larkvi/SimpleRTIDome/examples/v2/batch_010_onebirrcoin/010_09_rti.jpg

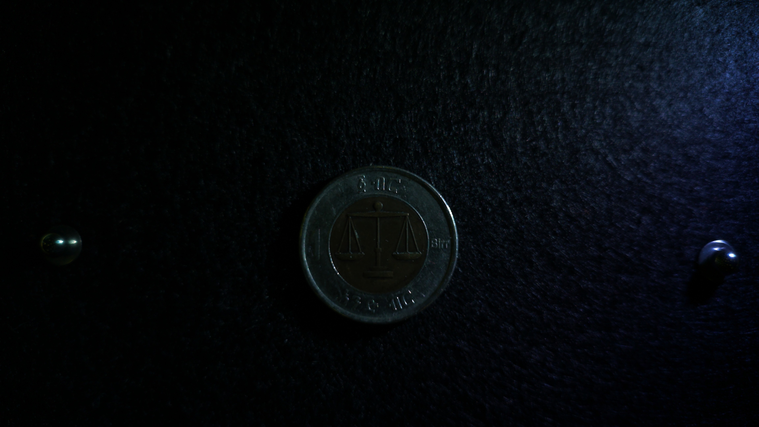
examples/v2/batch_010_onebirrcoin/010_09_rti.jpg
