larkvi/SimpleRTIDome/examples/v2/batch_010_onebirrcoin/010_17_rti.jpg

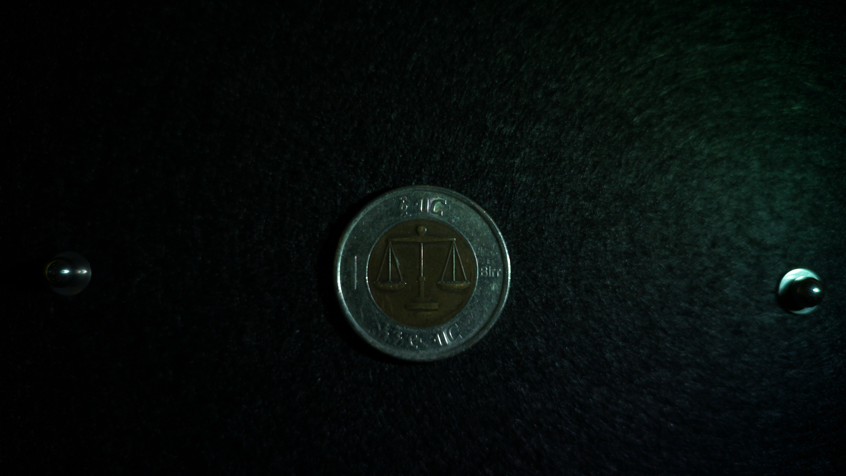
examples/v2/batch_010_onebirrcoin/010_17_rti.jpg
