larkvi/SimpleRTIDome/examples/v2/batch_010_onebirrcoin/010_19_rti.jpg

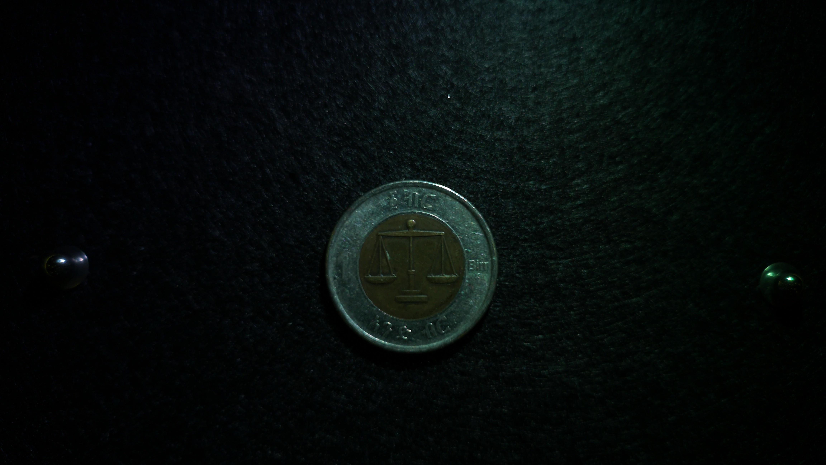
examples/v2/batch_010_onebirrcoin/010_19_rti.jpg
