larkvi/SimpleRTIDome/examples/v2/batch_010_onebirrcoin/010_22_rti.jpg

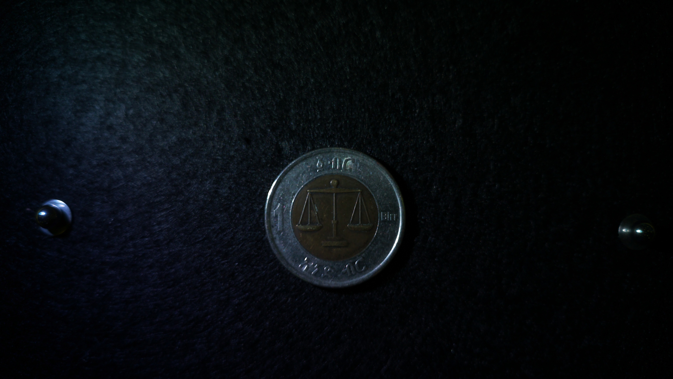
examples/v2/batch_010_onebirrcoin/010_22_rti.jpg
