larkvi/SimpleRTIDome/examples/v2/batch_010_onebirrcoin/010_40_rti.jpg

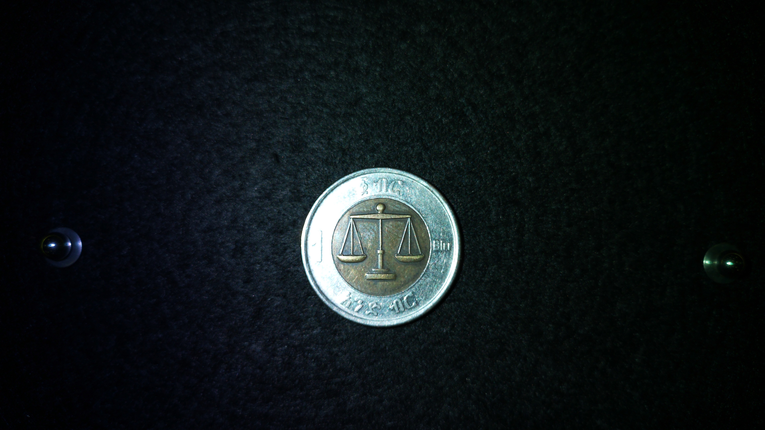
examples/v2/batch_010_onebirrcoin/010_40_rti.jpg
