larkvi/SimpleRTIDome/examples/v2/batch_010_onebirrcoin/output/plane_0_files/3/1_0.jpg

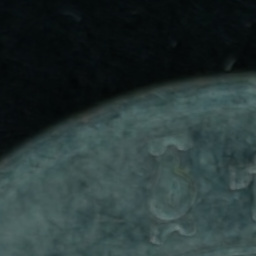
examples/v2/batch_010_onebirrcoin/output/plane_0_files/3/1_0.jpg
