larkvi/SimpleRTIDome/examples/v2/batch_010_onebirrcoin/output/plane_0_files/3/1_3.jpg

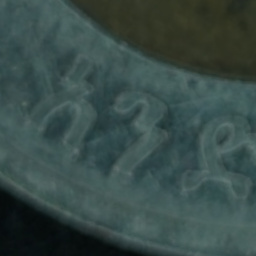
examples/v2/batch_010_onebirrcoin/output/plane_0_files/3/1_3.jpg
