larkvi/SimpleRTIDome/examples/v2/batch_010_onebirrcoin/output/plane_0_files/3/2_2.jpg

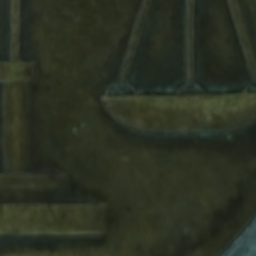
examples/v2/batch_010_onebirrcoin/output/plane_0_files/3/2_2.jpg
