larkvi/SimpleRTIDome/examples/v2/batch_010_onebirrcoin/output/plane_1_files/2/0_1.jpg

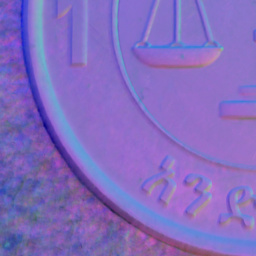
examples/v2/batch_010_onebirrcoin/output/plane_1_files/2/0_1.jpg
