larkvi/SimpleRTIDome/examples/v2/batch_010_onebirrcoin/output/plane_1_files/2/1_0.jpg

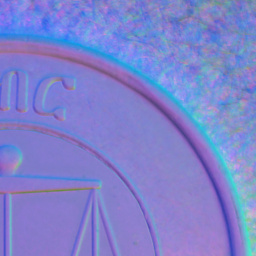
examples/v2/batch_010_onebirrcoin/output/plane_1_files/2/1_0.jpg
