larkvi/SimpleRTIDome/examples/v2/batch_010_onebirrcoin/output/plane_1_files/3/0_0.jpg

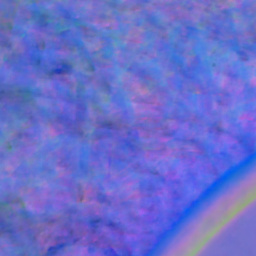
examples/v2/batch_010_onebirrcoin/output/plane_1_files/3/0_0.jpg
