larkvi/SimpleRTIDome/examples/v2/batch_010_onebirrcoin/output/plane_1_files/3/1_1.jpg

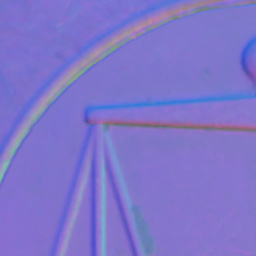
examples/v2/batch_010_onebirrcoin/output/plane_1_files/3/1_1.jpg
