larkvi/SimpleRTIDome/examples/v2/batch_010_onebirrcoin/output/plane_2.jpg

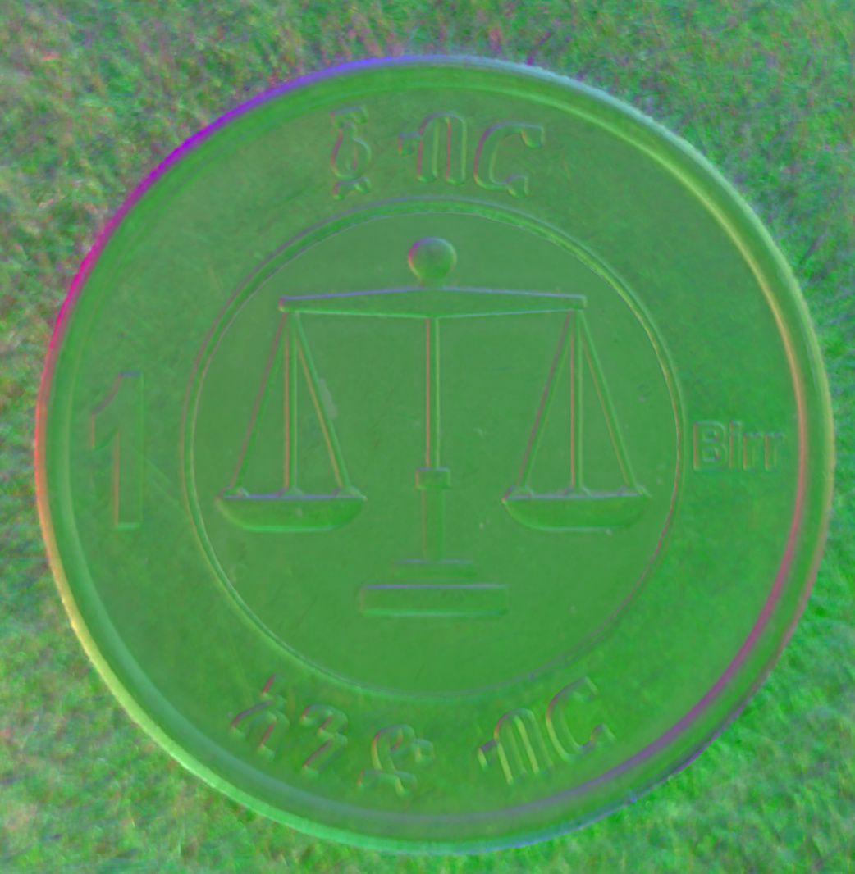
examples/v2/batch_010_onebirrcoin/output/plane_2.jpg
