larkvi/SimpleRTIDome/examples/v2/batch_010_onebirrcoin/output/plane_2_files/1/0_0.jpg

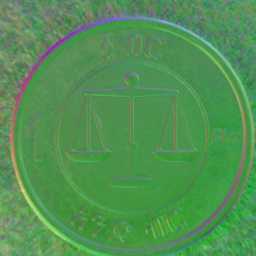
examples/v2/batch_010_onebirrcoin/output/plane_2_files/1/0_0.jpg
