larkvi/SimpleRTIDome/examples/v2/batch_011_donkey/011_12_rti.jpg

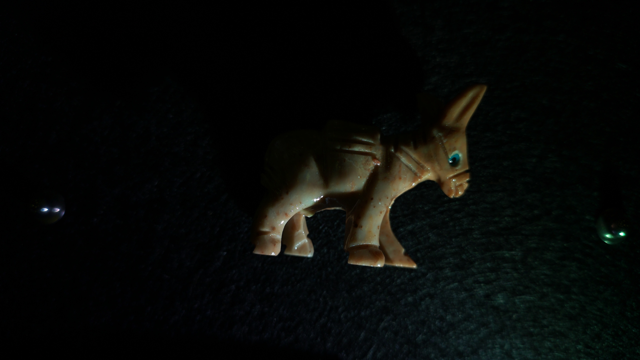
examples/v2/batch_011_donkey/011_12_rti.jpg
