larkvi/SimpleRTIDome/examples/v2/batch_011_donkey/011_21_rti.jpg

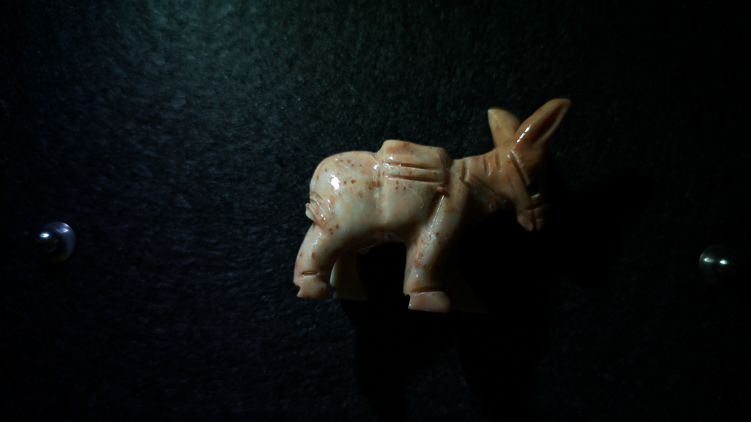
examples/v2/batch_011_donkey/011_21_rti.jpg
