larkvi/SimpleRTIDome/examples/v2/batch_011_donkey/011_23_rti.jpg

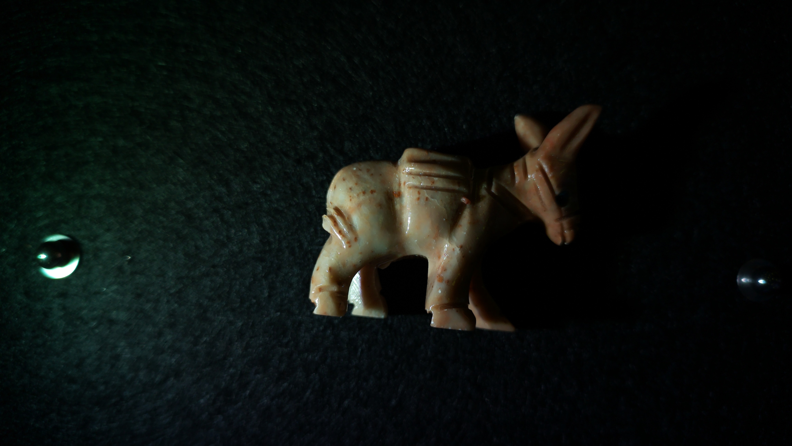
examples/v2/batch_011_donkey/011_23_rti.jpg
