larkvi/SimpleRTIDome/examples/v2/batch_011_donkey/011_31_rti.jpg

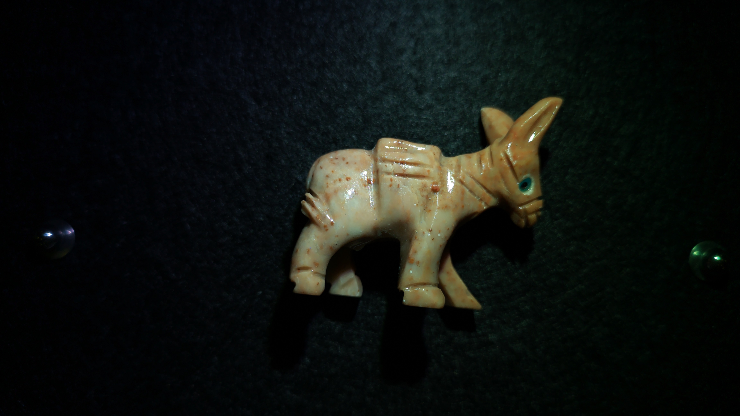
examples/v2/batch_011_donkey/011_31_rti.jpg
