larkvi/SimpleRTIDome/examples/v2/batch_011_donkey/011_32_rti.jpg

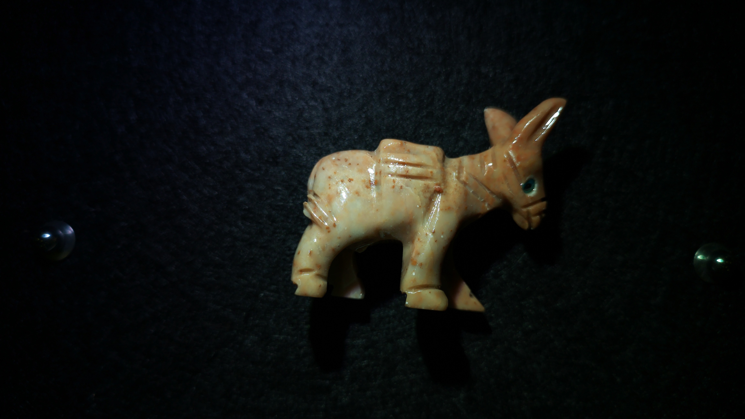
examples/v2/batch_011_donkey/011_32_rti.jpg
