larkvi/SimpleRTIDome/examples/v2/batch_011_donkey/output/plane_0_files/1/1_0.jpg

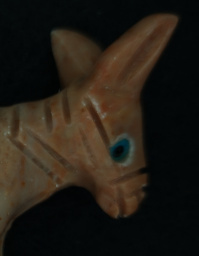
examples/v2/batch_011_donkey/output/plane_0_files/1/1_0.jpg
