larkvi/SimpleRTIDome/examples/v2/batch_011_donkey/output/plane_1.jpg

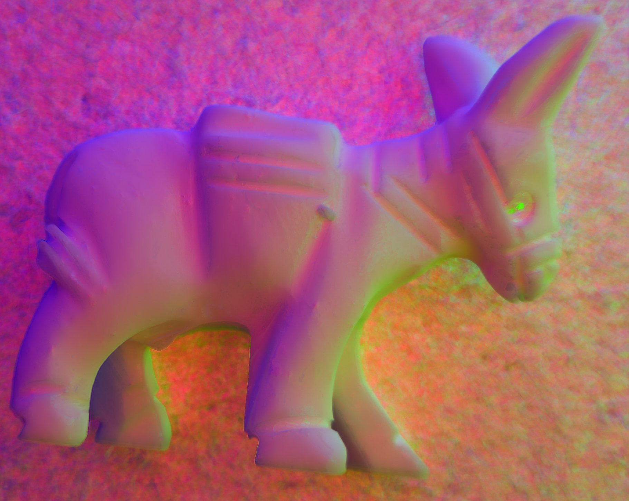
examples/v2/batch_011_donkey/output/plane_1.jpg
