larkvi/SimpleRTIDome/examples/v2/batch_011_donkey/output/plane_1_files/1/0_0.jpg

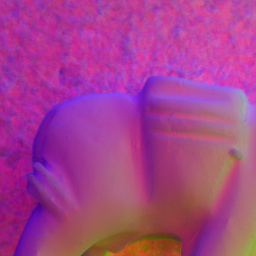
examples/v2/batch_011_donkey/output/plane_1_files/1/0_0.jpg
