larkvi/SimpleRTIDome/examples/v2/batch_011_donkey/output/plane_1_files/2/1_0.jpg

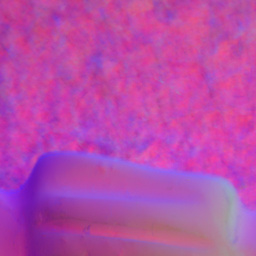
examples/v2/batch_011_donkey/output/plane_1_files/2/1_0.jpg
