larkvi/SimpleRTIDome/examples/v2/batch_011_donkey/output/plane_1_files/2/2_2.jpg

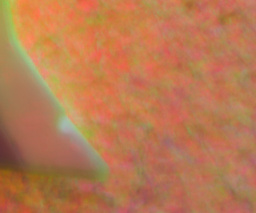
examples/v2/batch_011_donkey/output/plane_1_files/2/2_2.jpg
