larkvi/SimpleRTIDome/examples/v2/batch_011_donkey/output/plane_1_files/2/3_1.jpg

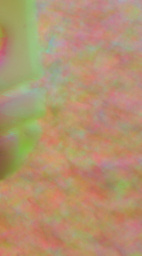
examples/v2/batch_011_donkey/output/plane_1_files/2/3_1.jpg
