larkvi/SimpleRTIDome/examples/v2/batch_011_donkey/output/plane_2_files/2/2_0.jpg

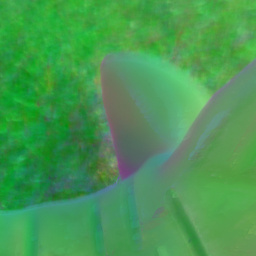
examples/v2/batch_011_donkey/output/plane_2_files/2/2_0.jpg
