larkvi/SimpleRTIDome/examples/v2/batch_011_donkey/sphere_1.png

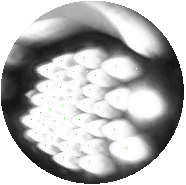
examples/v2/batch_011_donkey/sphere_1.png
