larkvi/SimpleRTIDome/examples/v2/batch_012_oddrock/012_29_rti.jpg

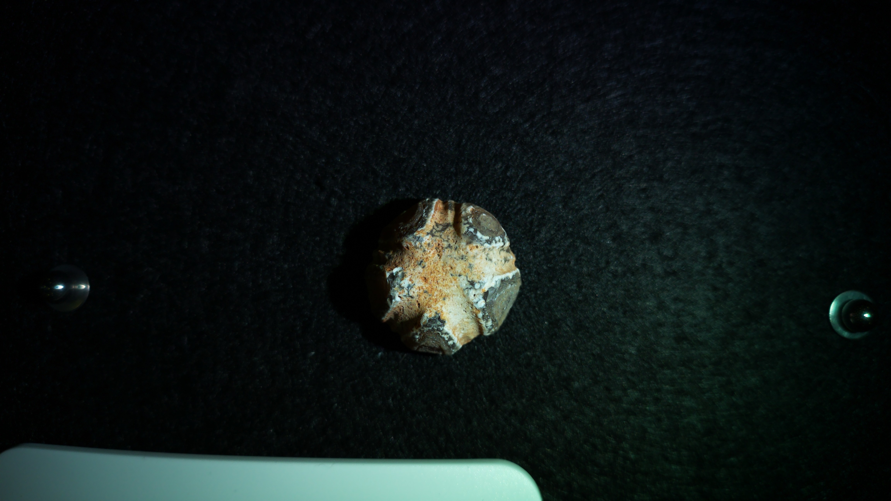
examples/v2/batch_012_oddrock/012_29_rti.jpg
