larkvi/SimpleRTIDome/examples/v2/batch_012_oddrock/output/plane_0.jpg

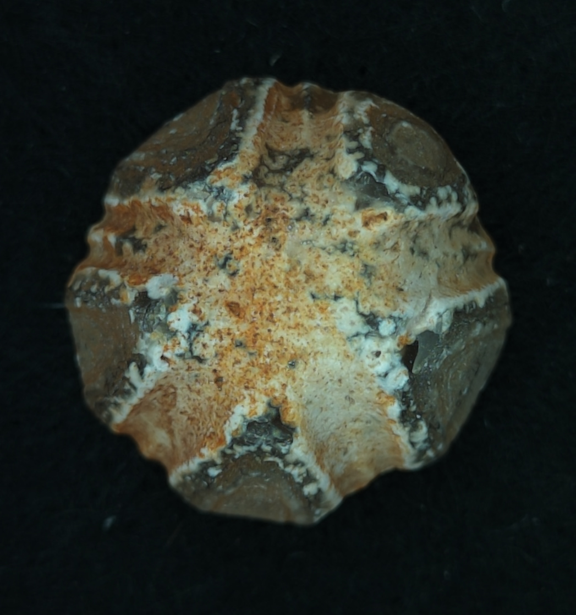
examples/v2/batch_012_oddrock/output/plane_0.jpg
