larkvi/SimpleRTIDome/examples/v2/batch_012_oddrock/output/plane_0_files/2/0_1.jpg

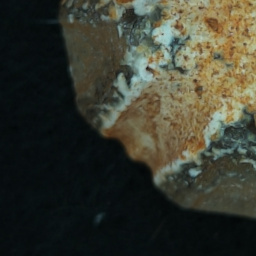
examples/v2/batch_012_oddrock/output/plane_0_files/2/0_1.jpg
