larkvi/SimpleRTIDome/examples/v2/batch_012_oddrock/output/plane_0_files/3/3_0.jpg

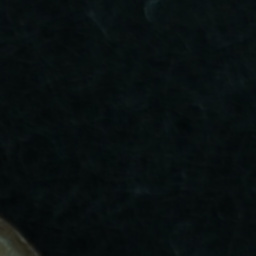
examples/v2/batch_012_oddrock/output/plane_0_files/3/3_0.jpg
