larkvi/SimpleRTIDome/examples/v2/batch_012_oddrock/output/plane_1_files/2/1_1.jpg

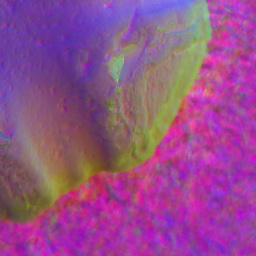
examples/v2/batch_012_oddrock/output/plane_1_files/2/1_1.jpg
