larkvi/SimpleRTIDome/examples/v2/batch_012_oddrock/output/plane_1_files/3/0_2.jpg

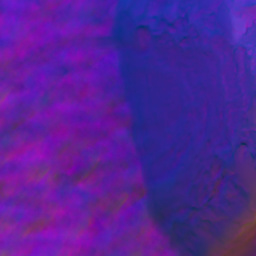
examples/v2/batch_012_oddrock/output/plane_1_files/3/0_2.jpg
