larkvi/SimpleRTIDome/examples/v2/batch_012_oddrock/output/plane_1_files/3/0_3.jpg

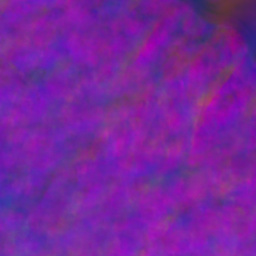
examples/v2/batch_012_oddrock/output/plane_1_files/3/0_3.jpg
