larkvi/SimpleRTIDome/examples/v2/batch_012_oddrock/output/plane_2_files/2/0_1.jpg

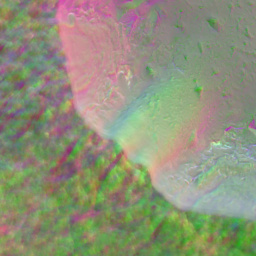
examples/v2/batch_012_oddrock/output/plane_2_files/2/0_1.jpg
