larkvi/SimpleRTIDome/examples/v2/batch_012_oddrock/output/plane_2_files/3/3_2.jpg

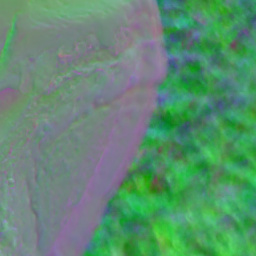
examples/v2/batch_012_oddrock/output/plane_2_files/3/3_2.jpg
