larkvi/SimpleRTIDome/examples/v2/batch_012_oddrock/sphere_1.png

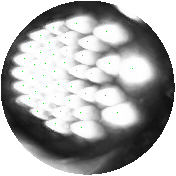
examples/v2/batch_012_oddrock/sphere_1.png
