larkvi/SimpleRTIDome/examples/v2/batch_013_fossil/013_09_rti.jpg

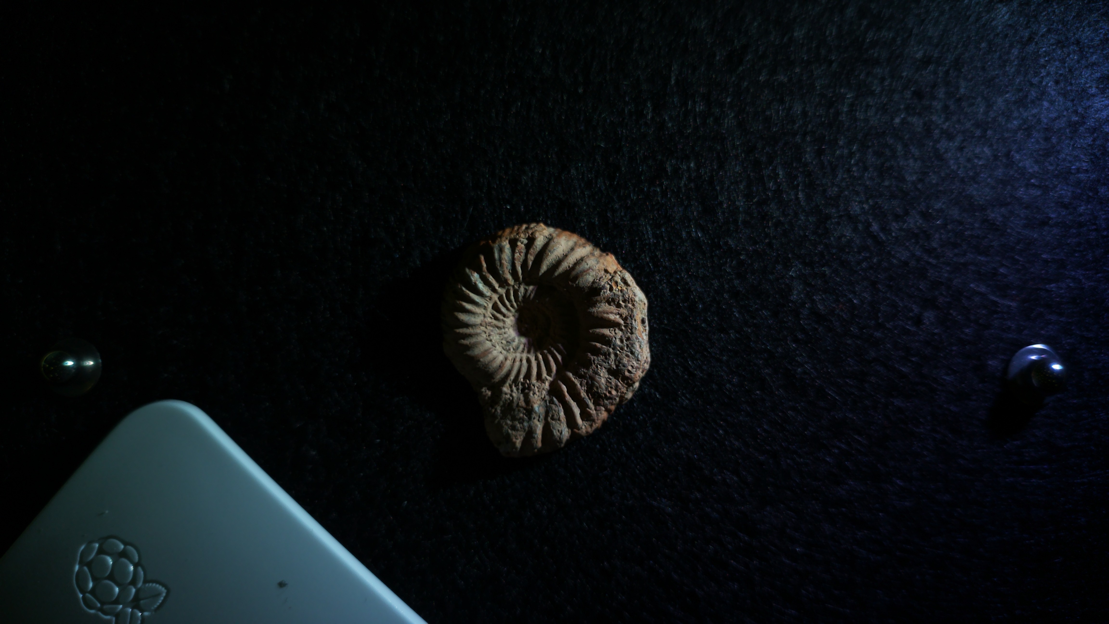
examples/v2/batch_013_fossil/013_09_rti.jpg
