larkvi/SimpleRTIDome/examples/v2/batch_013_fossil/013_19_rti.jpg

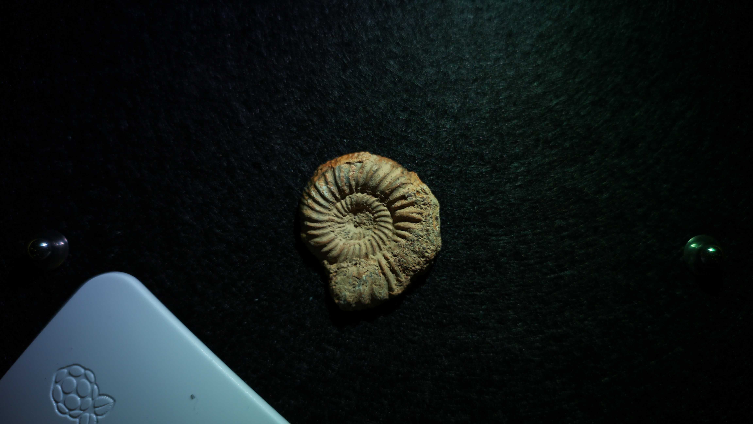
examples/v2/batch_013_fossil/013_19_rti.jpg
