larkvi/SimpleRTIDome/examples/v2/batch_013_fossil/013_21_rti.jpg

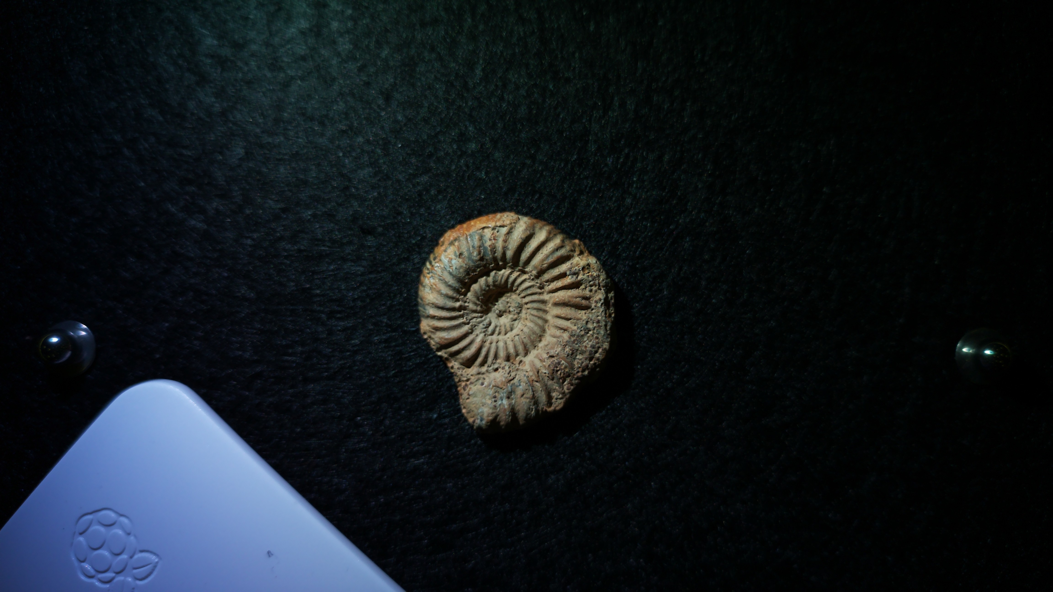
examples/v2/batch_013_fossil/013_21_rti.jpg
