larkvi/SimpleRTIDome/examples/v2/batch_013_fossil/output/plane_0.jpg

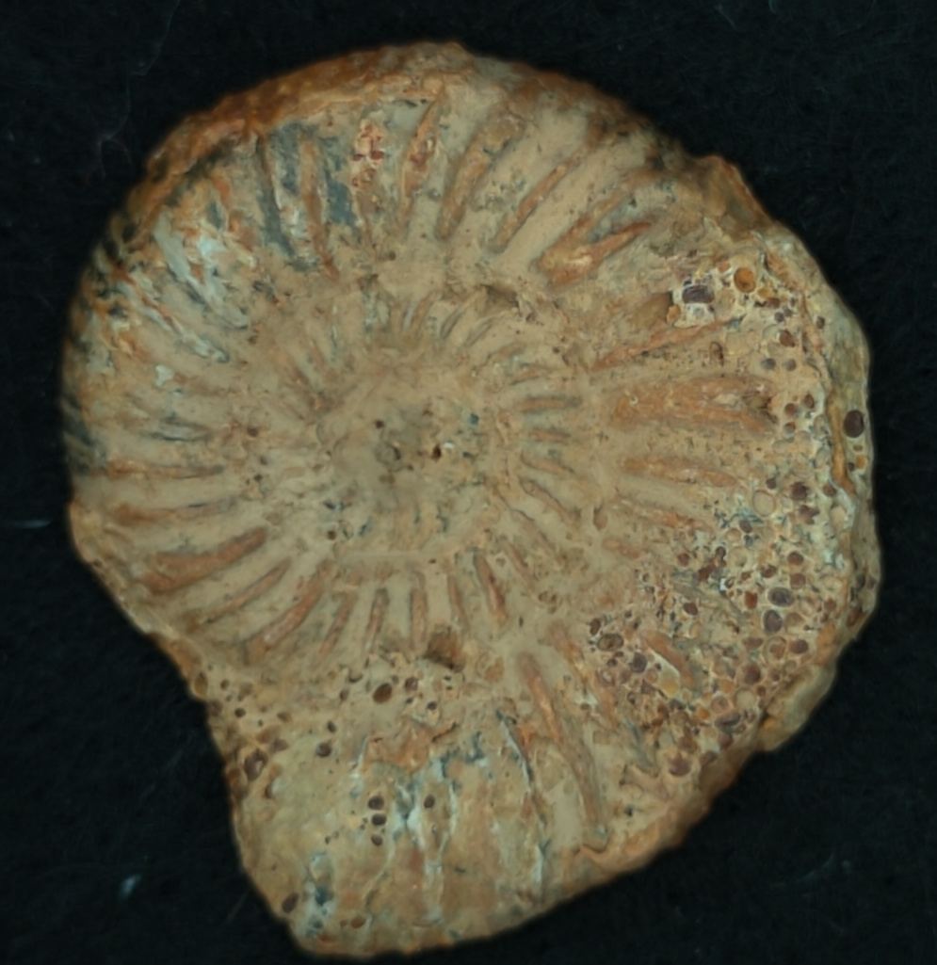
examples/v2/batch_013_fossil/output/plane_0.jpg
