larkvi/SimpleRTIDome/examples/v2/batch_013_fossil/output/plane_0_files/2/1_0.jpg

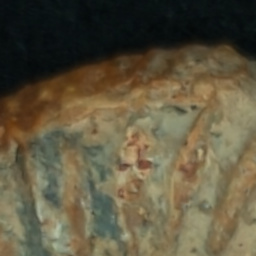
examples/v2/batch_013_fossil/output/plane_0_files/2/1_0.jpg
