larkvi/SimpleRTIDome/examples/v2/batch_013_fossil/output/plane_0_files/2/2_0.jpg

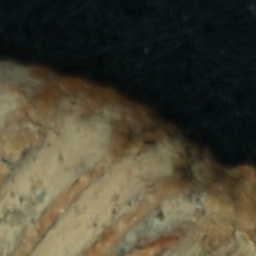
examples/v2/batch_013_fossil/output/plane_0_files/2/2_0.jpg
