larkvi/SimpleRTIDome/examples/v2/batch_013_fossil/output/plane_1_files/2/3_3.jpg

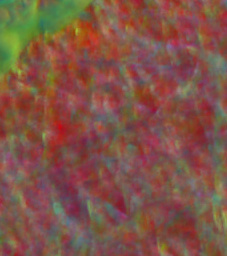
examples/v2/batch_013_fossil/output/plane_1_files/2/3_3.jpg
