larkvi/SimpleRTIDome/examples/v2/batch_013_fossil/output/plane_2_files/1/1_0.jpg

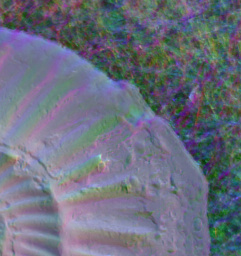
examples/v2/batch_013_fossil/output/plane_2_files/1/1_0.jpg
