larkvi/SimpleRTIDome/examples/v2/batch_013_fossil/output/plane_2_files/2/2_3.jpg

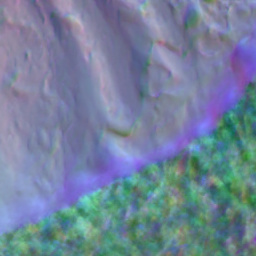
examples/v2/batch_013_fossil/output/plane_2_files/2/2_3.jpg
