larkvi/SimpleRTIDome/examples/v2/batch_013_fossil/sphere_0.png

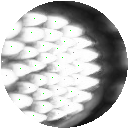
examples/v2/batch_013_fossil/sphere_0.png
